bsag/nine-nano/pcb/silkscreens/background.png

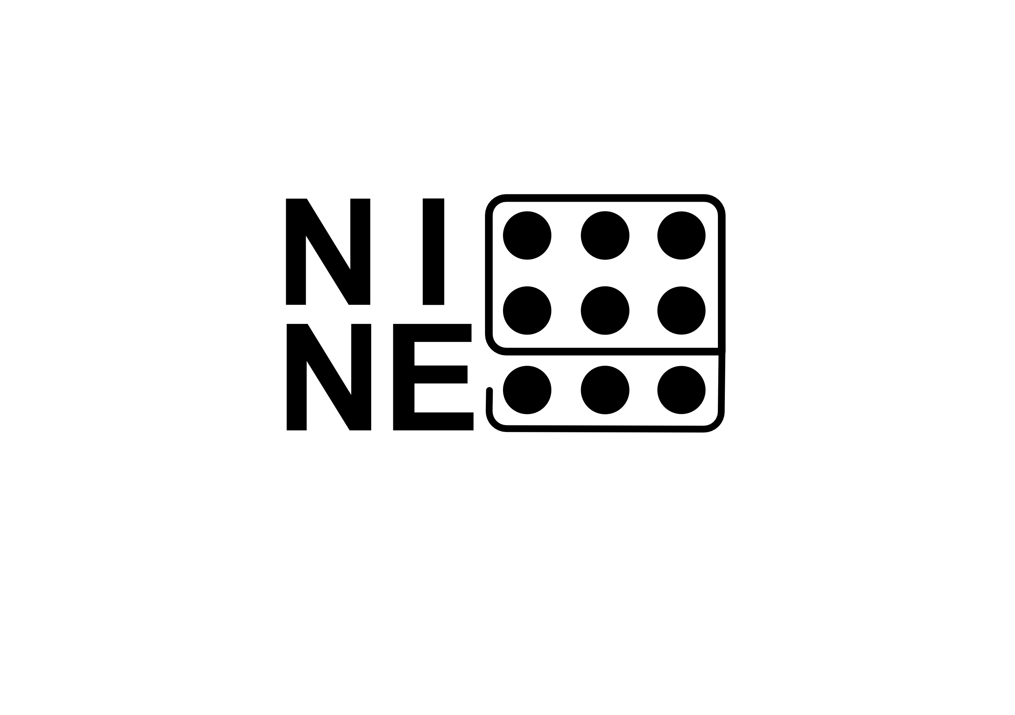
pcb/silkscreens/background.png
